zhelnio/AvrDDS/src/DDS/DDS/ddsGenerator.c

/*
 * dds.c
 *
 * Created: 07.01.2014 0:52:53
 *  Author: Stanislav
 */ 

#include "common.h"

// буфер для текущей табличной функции (заполнен подобием меандра для упрощения отладки)
uint8_t ddsBuffer[256] __attribute__((aligned(0x100))) = {
	0xff,0xff,0xff,0xff,0xff,0xff,0xff,0xff,0xff,0xff,0xff,0xff,0xff,0xff,0xff,0xff,
	0xff,0xff,0xff,0xff,0xff,0xff,0xff,0xff,0xff,0xff,0xff,0xff,0xff,0xff,0xff,0xff,
	0x00,0x00,0x00,0x00,0x00,0x00,0x00,0x00,0x00,0x00,0x00,0x00,0x00,0x00,0x00,0x00,
	0x00,0x00,0x00,0x00,0x00,0x00,0x00,0x00,0x00,0x00,0x00,0x00,0x00,0x00,0x00,0x00,
	0x00,0x00,0x00,0x00,0x00,0x00,0x00,0x00,0x00,0x00,0x00,0x00,0x00,0x00,0x00,0x00,
	0x00,0x00,0x00,0x00,0x00,0x00,0x00,0x00,0x00,0x00,0x00,0x00,0x00,0x00,0x00,0x00,
	0x00,0x00,0x00,0x00,0x00,0x00,0x00,0x00,0x00,0x00,0x00,0x00,0x00,0x00,0x00,0x00,
	0x00,0x00,0x00,0x00,0x00,0x00,0x00,0x00,0x00,0x00,0x00,0x00,0x00,0x00,0x00,0x00,
	0x00,0x00,0x00,0x00,0x00,0x00,0x00,0x00,0x00,0x00,0x00,0x00,0x00,0x00,0x00,0x00,
	0x00,0x00,0x00,0x00,0x00,0x00,0x00,0x00,0x00,0x00,0x00,0x00,0x00,0x00,0x00,0x00,
	0x00,0x00,0x00,0x00,0x00,0x00,0x00,0x00,0x00,0x00,0x00,0x00,0x00,0x00,0x00,0x00,
	0x7f,0x7f,0x7f,0x7f,0x7f,0x7f,0x7f,0x7f,0x7f,0x7f,0x7f,0x7f,0x7f,0x7f,0x7f,0x7f,
	0x7f,0x7f,0x7f,0x7f,0x7f,0x7f,0x7f,0x7f,0x7f,0x7f,0x7f,0x7f,0x7f,0x7f,0x7f,0x7f,
	0x00,0x00,0x00,0x00,0x00,0x00,0x00,0x00,0x00,0x00,0x00,0x00,0x00,0x00,0x00,0x00,
	0x00,0x00,0x00,0x00,0x00,0x00,0x00,0x00,0x00,0x00,0x00,0x00,0x00,0x00,0x00,0x00,
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

// настройки работы модуля
register volatile uint8_t ddsStopFlag asm("r10");	// регистр, в котором храниться флаг остановки генерации
													// генерация выполняется в main, флаг устанавливается в прерывании
const uint8_t ddsStopFlagBit = 0;					// номер стоп-бита флага остановки

union
{
	uint16_t val16;
	uint8_t  val8[2];
} ddsPhaseIncrementDelay;							// задержка перед переходом к следующей ячейке таблицы функции (буфера)

uint8_t ddsPhaseIncrementStep;						// шаг, с которым осуществляется переход к следующей ячейке таблицы функции (буфера)
const uint8_t maxDdsPhaseIncrementStep = 64;		// его минимальное и максимальное значения
const uint8_t minDdsPhaseIncrementStep = 1;

DdsSignalType ddsSignalType;						// тип сигнала
const DdsSignalType maxDdsSignalType = ddsKremlin;	// его минимальное и максимальное значения
const DdsSignalType minDdsSignalType = ddsSine;

ParameterMode ddsPhaseIncrementMode = modeView;		// режимы просмотра/редактирования параметров (просмотр, грубая настройка, точная настройка)
ParameterMode ddsSignalTypeMode = modeView;
ParameterMode ddsPhaseIncrementStepMode = modeView;

// Функция непосредственно выполняеющая проход по буферу с текущей таблице функции.
// Использует глобальные параметры шага/задержки.
// Для считывания новых настроек в прерывании устанавливается флаг остановки, что позволяет выйти из цикла внутри функции.
// После чего эта фукнция снова вызывается из main.
// Во время вызова проверяется минимальная задержка, если она = 0, значит генерация отключена.
void checkStopFlagAndDoDdsSignalOut()
{
	volatile uint8_t temp1 = 0, temp2 = 0;
	
	ddsStopFlag = (ddsPhaseIncrementDelay.val16 > 0) ? 0 : 1;

	asm volatile(
				" sbrc %[BYTE_EXIT], %[BIT_EXIT] "	"\n\t" \
				" rjmp Exit_%= "					"\n\t" \
		"Enter_%=: "								"\n\t" \
				" ld __tmp_reg__, z " 				"; 2 цикла	\n\t" \
				" out %[PPORT], __tmp_reg__ "		"; 1 цикл	\n\t" \
				" mov %[TMP_0], %[DELAY_0] "		"; 1 цикл   \n\t"      \
				" mov %[TMP_1], %[DELAY_1] "		"; 1 цикл   \n\t"      \
		"Delay_%=: "
				" subi %[TMP_0], 1"					"; 1 цикл  \n\t"      \
				" sbci %[TMP_1], 0"					"; 1 цикл  \n\t"      \
				" brne Delay_%="					"; 2 цикла при переходе по метке, иначе 1 цикл\n\t"      \
				" add r30, %[STEP] " 				"; 1 цикл	\n\t" \
				" sbrs %[BYTE_EXIT], %[BIT_EXIT] "	"; 1 цикл (условие ложно, не пропускаем) \n\t" \
				" rjmp Enter_%= "					"; 2 цикла. Итого: 12 (+4) циклов. \n\t" \
		"Exit_%=: "									"\n\t" \
				" out %[PPORT], __zero_reg__ "		"\n\t" \
		:
		:	[PPORT] "I" (_SFR_IO_ADDR(PORTD)),			\
			[ZPOINTER_REG] "z" (ddsBuffer),				\
			[BYTE_EXIT] "r" (ddsStopFlag),				\
			[BIT_EXIT] "I" (ddsStopFlagBit),			\
			[TMP_0] "r" (temp1),						\
			[TMP_1] "r" (temp2),						\
			[DELAY_0] "r" (ddsPhaseIncrementDelay.val8[0]),		\
			[DELAY_1] "r" (ddsPhaseIncrementDelay.val8[1]),		\
			[STEP] "r" (ddsPhaseIncrementStep)					\
	);
}

// функции работы с параметром Шаг
inline void ddsPhaseIncrementStepModeInc()
{
	ddsPhaseIncrementStepMode = (ddsPhaseIncrementStepMode == modeView) ? modeEditOrder0 : modeView;
}

inline void ddsPhaseIncrementStepInc()
{
	if(ddsPhaseIncrementStep == maxDdsPhaseIncrementStep)
		ddsPhaseIncrementStep = minDdsPhaseIncrementStep;
	else
		ddsPhaseIncrementStep++;
	
	eeprom_write_byte(&ddsPhaseIncrementStepEeprom, ddsPhaseIncrementStep);
}

inline void ddsPhaseIncrementStepDec()
{
	if(ddsPhaseIncrementStep == minDdsPhaseIncrementStep)
		ddsPhaseIncrementStep = maxDdsPhaseIncrementStep;
	else
		ddsPhaseIncrementStep--;
	
	eeprom_write_byte(&ddsPhaseIncrementStepEeprom, ddsPhaseIncrementStep);
}

// функции работы с параметром Тип сиглана
inline void ddsSignalTypeModeInc()
{
	ddsSignalTypeMode = (ddsSignalTypeMode == modeView) ? modeEditOrder0 : modeView;
}

inline void ddsSignalTypeInc()
{
	if(ddsSignalType == maxDdsSignalType)
		ddsSignalType = minDdsSignalType;
	else
		ddsSignalType++;
	
	eeprom_write_byte(&ddsSignalTypeEeprom, ddsSignalType);
}

inline void ddsSignalTypeDec()
{
	if(ddsSignalType == minDdsSignalType)
		ddsSignalType = maxDdsSignalType;
	else
		ddsSignalType--;
	
	eeprom_write_byte(&ddsSignalTypeEeprom, ddsSignalType);
}

// функции работы с параметром Задержка
inline void ddsPhaseIncrementDelayModeInc()
{
	if(ddsPhaseIncrementMode == modeView)
		ddsPhaseIncrementMode = modeEditOrder1;
	else
		ddsPhaseIncrementMode--;	
}

inline void ddsPhaseIncrementDelayInc()
{
	switch(ddsPhaseIncrementMode)
	{
		case modeEditOrder0:
			ddsPhaseIncrementDelay.val16++;
			break;
		
		case modeEditOrder1:
			ddsPhaseIncrementDelay.val8[1]++;
			break;
		
		default:	break;
	}
	
	eeprom_write_word(&ddsPhaseIncrementDelayEeprom, ddsPhaseIncrementDelay.val16);
}

inline void ddsPhaseIncrementDelayDec()
{
	switch(ddsPhaseIncrementMode)
	{
		case modeEditOrder0:
			ddsPhaseIncrementDelay.val16--;
			break;
		
		case modeEditOrder1:
			ddsPhaseIncrementDelay.val8[1]--;
			break;
		
		default:	break;
	}
	
	eeprom_write_word(&ddsPhaseIncrementDelayEeprom, ddsPhaseIncrementDelay.val16);
}

//функции преобразования значения параметра в строку
//все формулы расчитаны для тактовой частоты 16 Мгц
uint8_t ddsPhaseIncrementDelayToString(char target[])
{
	const uint8_t digitCount = 6;
	uint16_t temp = ddsPhaseIncrementDelay.val16;
	
	for(int8_t i = digitCount - 1; i >= 0; i--)
	{
		target[i] = '0' + temp % 10;
		temp = temp / 10;
	}
	
	return digitCount;
}

uint8_t ddsPhaseIncrementDelayToStringMU(char target[])
{
	const uint8_t valueDigitCountWithPoint = 8;
	const uint8_t valuePointPosition = 4;
	
	uint32_t temp = (192ul + (ddsPhaseIncrementDelay.val16 - 1ul) * 64ul)/ ddsPhaseIncrementStep;
	
	for(int8_t i = valueDigitCountWithPoint - 1; i >= 0; i--)
	{
		if(i == valuePointPosition)
		{
			target[i] = '.';
			continue;
		}
		
		target[i] = '0' + temp % 10;
		temp = temp / 10;
	}
	
	target[valueDigitCountWithPoint] = 'm';
	target[valueDigitCountWithPoint+1] = 's';
	
	return valueDigitCountWithPoint+2;
}

uint8_t ddsPhaseIncrementStepToString(char target[])
{
	const uint8_t digitCount = 2;
	uint8_t temp = ddsPhaseIncrementStep;
	
	for(int8_t i = digitCount - 1; i >= 0; i--)
	{
		target[i] = '0' + temp % 10;
		temp = temp / 10;
	}
	
	return digitCount;
}

uint8_t ddsSignalTypeToString(char target[])
{
	//порядок должен соответствовать таковому в enum
	char ValueName[][12] = {"Sine", "Triangle", "SawTooth", "RevSawTooth", "Tits", "ECG", "Kremlin", "None"};
	
	uint8_t strnum = ddsSignalType;
	uint8_t i = 0;
	
	while (ValueName[strnum][i] != '\0')
	{
		target[i] = ValueName[strnum][i];
		i++;
	}
	
	return i;
}

// public обработчик преобразования в строку
void DdsItemToString(void *menuItem, char target[])
{
	MenuItem *item = (MenuItem *) menuItem;
	uint8_t i = 0;
	
	
	
	switch(item->Id)
	{
		case mDds:
			i += MainItemWithStateToString(menuItem, target, (ddsPhaseIncrementDelay.val16 != 0));
			break;
		
		case mDdsDelay:
			i += PrepareItemValueString(menuItem,target);
			if(ddsPhaseIncrementDelay.val16 == 0)
				i += ui_strcpy(&target[i], "Offline");
			else
				i += ddsPhaseIncrementDelayToStringMU(&target[i]);
				i += AddModeToItemValueString(ddsPhaseIncrementMode, &target[i]);
			break;
		
		case mDdsSignal:
			i += PrepareItemValueString(menuItem,target);
			i += ddsSignalTypeToString(&target[i]);
			i += AddModeToItemValueString(ddsSignalTypeMode, &target[i]);
			break;
		
		case mDdsStep:	
			i += PrepareItemValueString(menuItem,target);	
			i += ddsPhaseIncrementStepToString(&target[i]);
			i += AddModeToItemValueString(ddsPhaseIncrementStepMode, &target[i]);
			break;
		
		default:;
	}
	target[i] = '\0';
}

// public обработчик событий от органов управления (кнопок)
ActionProcessed doDdsButtonAction (void *menuItem, eButton button)
{
	MenuItem *item = (MenuItem *) menuItem;
	
	// поведение зависит от текущего пунта меню
	switch(item->Id)
	{
		case mDdsDelay:
		switch(button)
		{
			case buttonRight:	ddsPhaseIncrementDelayModeInc();
								return aProcessedAll;
			case buttonLeft:	if(ddsPhaseIncrementMode == modeView) return aProcessedNone;
								ddsPhaseIncrementMode = modeView; return aProcessedAll;
			case buttonUp:		if(ddsPhaseIncrementMode == modeView) return aProcessedNone;
								ddsPhaseIncrementDelayInc(); return aProcessedAll;
			case buttonDown:	if(ddsPhaseIncrementMode == modeView) return aProcessedNone;
								ddsPhaseIncrementDelayDec(); return aProcessedAll;
			default: return aProcessedNone;
		}
		
		case mDdsSignal:
		switch (button)
		{
			case buttonRight:	ddsSignalTypeModeInc(); return aProcessedAll;
			case buttonLeft:	if(ddsSignalTypeMode == modeView) return aProcessedNone;
								ddsSignalTypeMode = modeView; return aProcessedAll;
			case buttonUp:		if(ddsSignalTypeMode == modeView) return aProcessedNone;
								ddsSignalTypeInc(); return aProcessedAll;
			case buttonDown:	if(ddsSignalTypeMode == modeView) return aProcessedNone;
								ddsSignalTypeDec(); return aProcessedAll;
			default: return aProcessedNone;
		}
		
		case mDdsStep:
		switch (button)
		{
			case buttonRight:	ddsPhaseIncrementStepModeInc();
								return aProcessedAll;
			case buttonLeft:	if(ddsPhaseIncrementStepMode == modeView) return aProcessedNone;
								ddsPhaseIncrementStepMode = modeView; return aProcessedAll;
			case buttonUp:		if(ddsPhaseIncrementStepMode == modeView) return aProcessedNone;
								ddsPhaseIncrementStepInc(); return aProcessedAll;
			case buttonDown:	if(ddsPhaseIncrementStepMode == modeView) return aProcessedNone;
								ddsPhaseIncrementStepDec(); return aProcessedAll;
			default: return aProcessedNone;
		}
		
		default: return aProcessedNone;
	}
}

// выполяет загрузку таблицы значений функции (буфера) из памяти программ
// либо генерацию этих значений
void ddsLoadData(DdsSignalType signalType)
{
	switch (signalType)
	{
		case ddsSine:
			memcpy_PF(ddsBuffer,&sine,sizeof ddsBuffer);
			break;
		
		case ddsTits:
			memcpy_PF(ddsBuffer,&tits,sizeof ddsBuffer);
			break;
		
		case ddsECG:
			memcpy_PF(ddsBuffer,&ecg,sizeof ddsBuffer);
			break;
		
		case ddsKremlin:
			memcpy_PF(ddsBuffer,&kremlin,sizeof ddsBuffer);
			break;
		
		case ddsTriangle:
			for(int i=0, j=0 ; i <= 127 ; i++)
			{
				ddsBuffer[i] = j;
				ddsBuffer[0xFF - i] = j;
				j +=2;
			}
			break;
		
		case ddsSawTooth:
			for(int i=0 ; i <= 255 ; i++)
				ddsBuffer[i] = i;
			break;
		
		case ddsRevSawTooth:
			for(int i=0 ; i <= 255 ; i++)
				ddsBuffer[i] = 0xFF - i;
			break;
		
		default:;
	}
}

// выполняет изменение настроек работы и выставляет флаг, по которому
// функция генерации будет перезапущена с новыми параметрами
void doDdsModeUpdateSettings()
{
	static DdsSignalType currentSignalType = ddsNone;
	
	if(currentSignalType != ddsSignalType)
	{
		ddsLoadData(ddsSignalType);
		currentSignalType = ddsSignalType;
	}
	
	ddsStopFlag = 1;
}

// public обработчик событий изменения режима работы
void doDdsModeAction(void *menuItem, eAction action)
{	
	if(action == onChange)
		doDdsModeUpdateSettings();
}

// public загрузка настроек модуля при включении устройства
void loadDdsSettings()
{	
	ddsPhaseIncrementDelay.val16 = eeprom_read_word(&ddsPhaseIncrementDelayEeprom);
	
	ddsPhaseIncrementStep = eeprom_read_byte(&ddsPhaseIncrementStepEeprom);
	if(ddsPhaseIncrementStep > maxDdsPhaseIncrementStep || ddsPhaseIncrementStep < minDdsPhaseIncrementStep)
		ddsPhaseIncrementStep = minDdsPhaseIncrementStep;
		
	ddsSignalType = eeprom_read_byte(&ddsSignalTypeEeprom);
	if(ddsSignalType > maxDdsSignalType || ddsSignalType < minDdsSignalType)
		ddsSignalType = minDdsSignalType;

	doDdsModeUpdateSettings();
}
